emax73/Ka-Radio32/components/fdk-aac-oreo-m8/libAACenc/src/aacenc.cpp

/* -----------------------------------------------------------------------------------------------------------
Software License for The Fraunhofer FDK AAC Codec Library for Android

© Copyright  1995 - 2015 Fraunhofer-Gesellschaft zur Förderung der angewandten Forschung e.V.
  All rights reserved.

 1.    INTRODUCTION
The Fraunhofer FDK AAC Codec Library for Android ("FDK AAC Codec") is software that implements
the MPEG Advanced Audio Coding ("AAC") encoding and decoding scheme for digital audio.
This FDK AAC Codec software is intended to be used on a wide variety of Android devices.

AAC's HE-AAC and HE-AAC v2 versions are regarded as today's most efficient general perceptual
audio codecs. AAC-ELD is considered the best-performing full-bandwidth communications codec by
independent studies and is widely deployed. AAC has been standardized by ISO and IEC as part
of the MPEG specifications.

Patent licenses for necessary patent claims for the FDK AAC Codec (including those of Fraunhofer)
may be obtained through Via Licensing (www.vialicensing.com) or through the respective patent owners
individually for the purpose of encoding or decoding bit streams in products that are compliant with
the ISO/IEC MPEG audio standards. Please note that most manufacturers of Android devices already license
these patent claims through Via Licensing or directly from the patent owners, and therefore FDK AAC Codec
software may already be covered under those patent licenses when it is used for those licensed purposes only.

Commercially-licensed AAC software libraries, including floating-point versions with enhanced sound quality,
are also available from Fraunhofer. Users are encouraged to check the Fraunhofer website for additional
applications information and documentation.

2.    COPYRIGHT LICENSE

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
You must retain the complete text of this software license in redistributions of the FDK AAC Codec or
your modifications thereto in source code form.

You must retain the complete text of this software license in the documentation and/or other materials
provided with redistributions of the FDK AAC Codec or your modifications thereto in binary form.
You must make available free of charge copies of the complete source code of the FDK AAC Codec and your
modifications thereto to recipients of copies in binary form.

The name of Fraunhofer may not be used to endorse or promote products derived from this library without
prior written permission.

You may not charge copyright license fees for anyone to use, copy or distribute the FDK AAC Codec
software or your modifications thereto.

Your modified versions of the FDK AAC Codec must carry prominent notices stating that you changed the software
and the date of any change. For modified versions of the FDK AAC Codec, the term
"Fraunhofer FDK AAC Codec Library for Android" must be replaced by the term
"Third-Party Modified Version of the Fraunhofer FDK AAC Codec Library for Android."

3.    NO PATENT LICENSE

NO EXPRESS OR IMPLIED LICENSES TO ANY PATENT CLAIMS, including without limitation the patents of Fraunhofer,
ARE GRANTED BY THIS SOFTWARE LICENSE. Fraunhofer provides no warranty of patent non-infringement with
respect to this software.

You may use this FDK AAC Codec software or modifications thereto only for purposes that are authorized
by appropriate patent licenses.

4.    DISCLAIMER

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
5.    CONTACT INFORMATION

Fraunhofer Institute for Integrated Circuits IIS
Attention: Audio and Multimedia Departments - FDK AAC LL
Am Wolfsmantel 33
91058 Erlangen, Germany

www.iis.fraunhofer.de/amm
amm-info@iis.fraunhofer.de
----------------------------------------------------------------------------------------------------------- */

/***************************  Fast MPEG AAC Audio Encoder  **********************

   Initial author:       M. Schug / A. Groeschel
   contents/description: fast aac coder functions

******************************************************************************/

#include "aacenc.h"

#include "bitenc.h"
#include "interface.h"
#include "psy_configuration.h"
#include "psy_main.h"
#include "qc_main.h"
#include "bandwidth.h"
#include "channel_map.h"
#include "tns_func.h"
#include "aacEnc_ram.h"

#include "genericStds.h"




#define MIN_BUFSIZE_PER_EFF_CHAN 6144

INT FDKaacEnc_CalcBitsPerFrame(
        const INT bitRate,
        const INT frameLength,
        const INT samplingRate
        )
{
    int shift = 0;
    while ((frameLength & ~((1 << (shift + 1)) - 1)) == frameLength
        && (samplingRate & ~((1 << (shift + 1)) - 1)) == samplingRate)
    {
      shift++;
    }

    return (bitRate*(frameLength>>shift)) / (samplingRate>>shift);
}

INT FDKaacEnc_CalcBitrate(
        const INT bitsPerFrame,
        const INT frameLength,
        const INT samplingRate
        )
{
    int shift = 0;
    while ((frameLength & ~((1 << (shift + 1)) - 1)) == frameLength
        && (samplingRate & ~((1 << (shift + 1)) - 1)) == samplingRate)
    {
      shift++;
    }

    return (bitsPerFrame * (samplingRate>>shift)) / ( frameLength>>shift) ;

}

static AAC_ENCODER_ERROR FDKaacEnc_InitCheckAncillary(INT bitRate,
                                                      INT framelength,
                                                      INT ancillaryRate,
                                                      INT *ancillaryBitsPerFrame,
                                                      INT sampleRate);

INT FDKaacEnc_LimitBitrate(
        HANDLE_TRANSPORTENC hTpEnc,
        INT coreSamplingRate,
        INT frameLength,
        INT nChannels,
        INT nChannelsEff,
        INT bitRate,
        INT averageBits,
        INT *pAverageBitsPerFrame,
        INT bitrateMode,
        INT nSubFrames
        )
{
  INT transportBits, prevBitRate, averageBitsPerFrame, shift = 0, iter=0;

  while ( (frameLength & ~((1<<(shift+1))-1)) == frameLength
    && (coreSamplingRate & ~((1<<(shift+1))-1)) == coreSamplingRate )
  {
    shift ++;
  }

  do {
    prevBitRate = bitRate;
     averageBitsPerFrame = (bitRate*(frameLength>>shift)) / (coreSamplingRate>>shift) / nSubFrames;

    if (pAverageBitsPerFrame != NULL) {
      *pAverageBitsPerFrame = averageBitsPerFrame;
    }

    if (hTpEnc != NULL) {
      transportBits = transportEnc_GetStaticBits(hTpEnc, averageBitsPerFrame);
    } else {
      /* Assume some worst case */
      transportBits = 208;
    }

    bitRate = FDKmax(bitRate, ((((40 * nChannels) + transportBits) * (coreSamplingRate)) / frameLength) );
    FDK_ASSERT(bitRate >= 0);

    bitRate = FDKmin(bitRate, ((nChannelsEff * MIN_BUFSIZE_PER_EFF_CHAN)*(coreSamplingRate>>shift)) / (frameLength>>shift)) ;
    FDK_ASSERT(bitRate >= 0);

  } while (prevBitRate != bitRate && iter++ < 3) ;

  return bitRate;
}


typedef struct
{
  AACENC_BITRATE_MODE bitrateMode;
  int chanBitrate[2]; /* mono/stereo settings */
} CONFIG_TAB_ENTRY_VBR;

static const CONFIG_TAB_ENTRY_VBR configTabVBR[] = {
  {AACENC_BR_MODE_CBR,   {     0,     0}} ,
  {AACENC_BR_MODE_VBR_1, { 32000, 20000}} ,
  {AACENC_BR_MODE_VBR_2, { 40000, 32000}} ,
  {AACENC_BR_MODE_VBR_3, { 56000, 48000}} ,
  {AACENC_BR_MODE_VBR_4, { 72000, 64000}} ,
  {AACENC_BR_MODE_VBR_5, {112000, 96000}}
};

/*-----------------------------------------------------------------------------

     functionname: FDKaacEnc_GetVBRBitrate
     description:  Get VBR bitrate from vbr quality
     input params: int vbrQuality (VBR0, VBR1, VBR2)
                   channelMode
     returns:      vbr bitrate

 ------------------------------------------------------------------------------*/
INT FDKaacEnc_GetVBRBitrate(INT bitrateMode, CHANNEL_MODE channelMode)
{
  INT bitrate = 0;
  INT monoStereoMode = 0; /* default mono */

  if (FDKaacEnc_GetMonoStereoMode(channelMode)==EL_MODE_STEREO) {
      monoStereoMode = 1;
  }

  switch((AACENC_BITRATE_MODE)bitrateMode){
  case AACENC_BR_MODE_VBR_1:
  case AACENC_BR_MODE_VBR_2:
  case AACENC_BR_MODE_VBR_3:
  case AACENC_BR_MODE_VBR_4:
  case AACENC_BR_MODE_VBR_5:
    bitrate = configTabVBR[bitrateMode].chanBitrate[monoStereoMode];
    break;
  case AACENC_BR_MODE_INVALID:
  case AACENC_BR_MODE_CBR:
  case AACENC_BR_MODE_SFR:
  case AACENC_BR_MODE_FF:
  default:
    bitrate = 0;
    break;
  }

  /* convert channel bitrate to overall bitrate*/
  bitrate *= FDKaacEnc_GetChannelModeConfiguration(channelMode)->nChannelsEff;

  return bitrate;
}

/**
 * \brief  Convert encoder bitreservoir value for transport library.
 *
 * \param hAacEnc               Encoder handle
 *
 * \return  Corrected bitreservoir level used in transport library.
 */
static INT FDKaacEnc_EncBitresToTpBitres(
        const HANDLE_AAC_ENC      hAacEnc
        )
{
  INT transporBitreservoir = 0;

  switch (hAacEnc->bitrateMode) {
    case AACENC_BR_MODE_CBR:
      transporBitreservoir = hAacEnc->qcKernel->bitResTot; /* encoder bitreservoir level */
      break;
    case AACENC_BR_MODE_VBR_1:
    case AACENC_BR_MODE_VBR_2:
    case AACENC_BR_MODE_VBR_3:
    case AACENC_BR_MODE_VBR_4:
    case AACENC_BR_MODE_VBR_5:
      transporBitreservoir = FDK_INT_MAX; /* signal variable bitrate */
      break;
    case AACENC_BR_MODE_FF:
    case AACENC_BR_MODE_SFR:
      transporBitreservoir = 0;           /* super framing and fixed framing */
      break;                              /* without bitreservoir signaling */
    default:
    case AACENC_BR_MODE_INVALID:
      transporBitreservoir = 0;           /* invalid configuration*/
      FDK_ASSERT(0);
  }

  if (hAacEnc->config->audioMuxVersion==2) {
    transporBitreservoir = MIN_BUFSIZE_PER_EFF_CHAN * hAacEnc->channelMapping.nChannelsEff;
  }

  return transporBitreservoir;
}

/*-----------------------------------------------------------------------------

     functionname: FDKaacEnc_AacInitDefaultConfig
     description:  gives reasonable default configuration
     returns:      ---

 ------------------------------------------------------------------------------*/
void FDKaacEnc_AacInitDefaultConfig(AACENC_CONFIG *config)
{
    /* make thepre initialization of the structs flexible */
    FDKmemclear(config, sizeof(AACENC_CONFIG));

    /* default ancillary */
    config->anc_Rate = 0;         /* no ancillary data */
    config->ancDataBitRate = 0;   /* no additional consumed bitrate */

    /* default configurations */
    config->bitRate         = -1;                   /* bitrate must be set*/
    config->averageBits     = -1;                   /* instead of bitrate/s we can configure bits/superframe */
    config->bitrateMode     = 0;
    config->bandWidth       = 0;                    /* get bandwidth from table */
    config->useTns          = TNS_ENABLE_MASK;      /* tns enabled completly */
    config->usePns          = 1;                    /* depending on channelBitrate this might be set to 0 later */
    config->useIS           = 1;                    /* Intensity Stereo Configuration */
    config->framelength     = -1;                   /* Framesize not configured */
    config->syntaxFlags     = 0;                    /* default syntax with no specialities */
    config->epConfig        = -1;                   /* no ER syntax -> no additional error protection */
    config->nSubFrames      = 1;                    /* default, no sub frames */
    config->channelOrder    = CH_ORDER_MPEG;        /* Use MPEG channel ordering. */
    config->channelMode     = MODE_UNKNOWN;
    config->minBitsPerFrame = -1;                   /* minum number of bits in each AU */
    config->maxBitsPerFrame = -1;                   /* minum number of bits in each AU */
    config->bitreservoir    = -1;                   /* default, uninitialized value */
    config->audioMuxVersion = -1;                   /* audio mux version not configured */

    /* init tabs in fixpoint_math */
    InitLdInt();
    InitInvSqrtTab();
}


/*---------------------------------------------------------------------------

    functionname: FDKaacEnc_Open
    description:  allocate and initialize a new encoder instance
    returns:      error code

  ---------------------------------------------------------------------------*/
AAC_ENCODER_ERROR FDKaacEnc_Open(HANDLE_AAC_ENC  *phAacEnc,
                                 const INT        nElements,
                                 const INT        nChannels,
                                 const INT        nSubFrames)
{
  AAC_ENCODER_ERROR ErrorStatus;
  AAC_ENC           *hAacEnc = NULL;
  UCHAR             *dynamicRAM = NULL;

  if (phAacEnc==NULL) {
    return AAC_ENC_INVALID_HANDLE;
  }

  /* allocate encoder structure */
  hAacEnc = GetRam_aacEnc_AacEncoder();
  if (hAacEnc == NULL) {
    ErrorStatus = AAC_ENC_NO_MEMORY;
    goto bail;
  }
  FDKmemclear(hAacEnc, sizeof(AAC_ENC));

  hAacEnc->dynamic_RAM = GetAACdynamic_RAM();
  dynamicRAM = (UCHAR*)hAacEnc->dynamic_RAM;

  /* allocate the Psy aud Psy Out structure */
   ErrorStatus = FDKaacEnc_PsyNew(&hAacEnc->psyKernel,
                                  nElements,
                                  nChannels
                                 ,dynamicRAM
                                 );
   if (ErrorStatus != AAC_ENC_OK)
     goto bail;

   ErrorStatus = FDKaacEnc_PsyOutNew(hAacEnc->psyOut,
                                     nElements,
                                     nChannels,
                                     nSubFrames
                                    ,dynamicRAM
                                    );
   if (ErrorStatus != AAC_ENC_OK)
     goto bail;

  /* allocate the Q&C Out structure */
  ErrorStatus = FDKaacEnc_QCOutNew(hAacEnc->qcOut,
                                   nElements,
                                   nChannels,
                                   nSubFrames
                                  ,dynamicRAM
                                   );
  if (ErrorStatus != AAC_ENC_OK)
    goto bail;

  /* allocate the Q&C kernel */
  ErrorStatus = FDKaacEnc_QCNew(&hAacEnc->qcKernel,
                                 nElements
                                ,dynamicRAM
                                );
  if (ErrorStatus != AAC_ENC_OK)
    goto bail;

  hAacEnc->maxChannels = nChannels;
  hAacEnc->maxElements = nElements;
  hAacEnc->maxFrames   = nSubFrames;

bail:
  *phAacEnc = hAacEnc;
  return ErrorStatus;
}
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
