emax73/Ka-Radio32/components/ucglib/csrc/ucg_karadio32_fonts.c

/*
  Fontname: ixed
  Copyright: Public domain font.  Share and enjoy.
  Glyphs: 224/256
  BBX Build Mode: 0
*/
#include "ucg.h"
const ucg_fntpgm_uint8_t ucg_font_5x7_gr[2005] UCG_FONT_SECTION("ucg_font_5x7_gr") = {
  224,0,2,2,3,3,3,4,5,6,7,0,255,6,255,6,
  0,1,22,2,56,32,5,0,177,2,33,7,177,177,50,82,
  0,34,7,91,183,146,172,0,35,10,45,177,86,13,85,13,
  85,1,36,10,45,177,182,106,176,65,74,11,37,9,52,177,
  146,65,236,13,2,38,9,44,177,22,83,172,98,10,39,5,
  153,183,50,40,7,114,177,166,154,1,41,8,114,177,18,83,
  165,0,42,8,107,177,146,170,213,0,43,10,45,177,154,81,
  28,50,163,8,44,7,91,175,166,74,0,45,6,12,181,50,
  2,46,6,82,177,50,2,47,7,36,179,14,98,27,48,8,
  115,177,86,185,42,0,49,7,115,177,150,100,107,50,10,52,
  177,166,98,6,177,28,1,51,11,52,177,50,50,72,26,201,
  164,0,52,10,52,177,26,85,53,98,6,9,53,10,52,177,
  50,52,216,72,38,5,54,10,52,177,166,50,88,81,38,5,
  55,12,52,177,50,50,136,25,196,12,34,0,56,10,52,177,
  166,98,82,81,38,5,57,10,52,177,166,162,76,27,36,5,
  58,7,106,177,50,226,8,59,8,51,175,102,35,85,2,60,
  9,107,177,154,106,144,65,0,61,8,28,179,50,50,26,1,
  62,9,107,177,146,65,6,169,4,63,9,115,177,214,76,25,
  38,0,64,9,52,177,166,162,186,145,2,65,9,52,177,166,
  162,28,83,6,66,10,52,177,178,226,72,81,142,4,67,11,
  52,177,166,162,6,25,196,164,0,68,9,52,177,178,162,115,
  36,0,69,11,52,177,50,52,88,25,100,48,2,70,11,52,
  177,50,52,88,25,100,144,1,71,10,52,177,166,162,6,105,
  166,1,72,9,52,177,18,229,152,102,0,73,7,115,177,178,
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
  124,54,75,230,151,202,26,82,14,149,132,22,67,146,217,6,
  165,84,201,180,0,83,13,149,132,54,75,38,166,107,168,37,
  11,0,84,10,149,132,22,131,20,246,19,0,85,10,149,132,
  22,153,191,37,11,0,86,14,149,132,22,153,91,82,74,162,
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
/*
  Fontname: ixed
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
